Seguranca-do-Trabalho/snes-smart-home/hardware/01_SNES_BUS_AND_CIC.kicad_sch

## KiCad design hardware/01_SNES_BUS_AND_CIC.kicad_sch (2026-09-11)

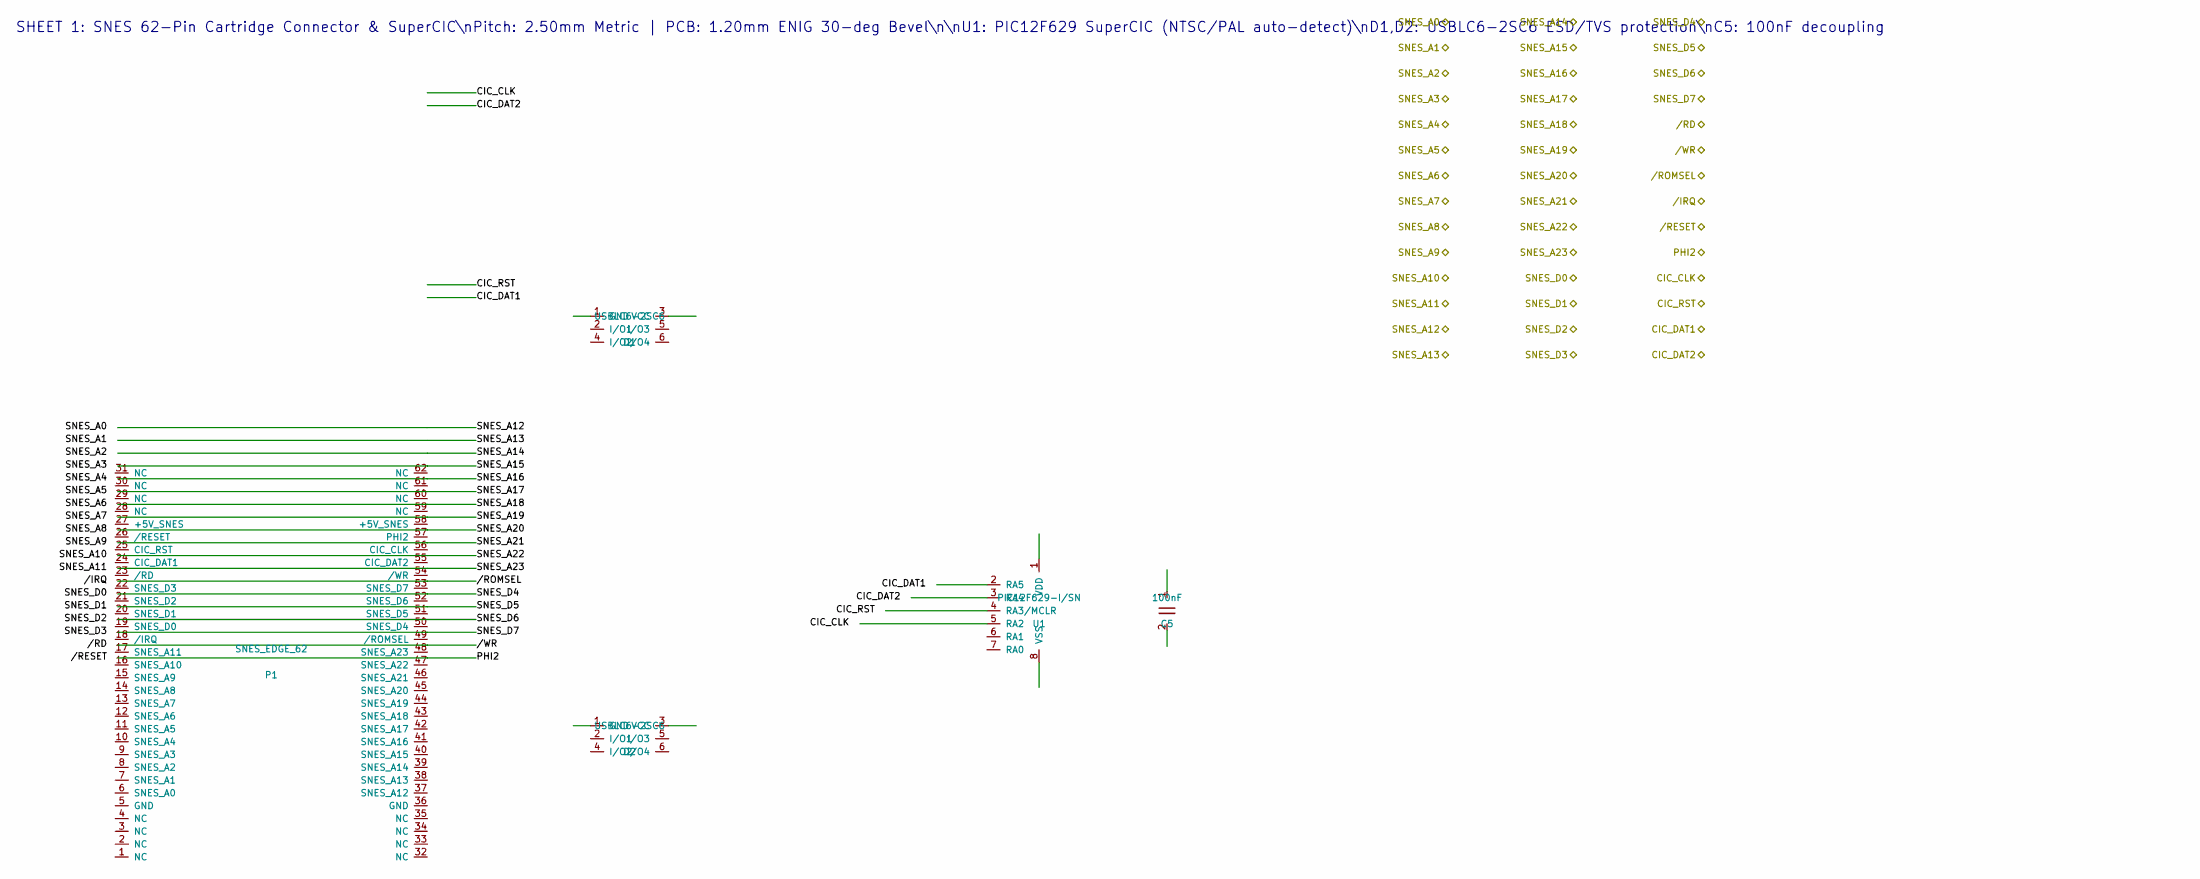
[picture p6: schematic 01_SNES_BUS_AND_CIC.kicad_sch]

Parts:
C5: 100nF; C_0402_1005Metric; LCSC C14663
D1, D2: USBLC6-2SC6; SOT-23-6_Handsoldering; LCSC C7519
P1: SNES_EDGE_62; SNES_CartridgeEdge_62Pin_2.50mm; LCSC Custom
U1: PIC12F629-I/SN; SOIC-8_3.9x4.9mm_P1.27mm; LCSC C20967

Notes on the sheet:
SHEET 1: SNES 62-Pin Cartridge Connector & SuperCIC\nPitch: 2.50mm Metric | PCB: 1.20mm ENIG 30-deg Bevel\n\nU1: PIC12F629 SuperCIC (NTSC/PAL auto-detect)\nD1,D2: USBLC6-2SC6 ESD/TVS protection\nC5: 100nF decoupling
