Seguranca-do-Trabalho/snes-smart-home/hardware/02_LEVEL_SHIFTERS_AND_FLASH.kicad_sch

## KiCad design hardware/02_LEVEL_SHIFTERS_AND_FLASH.kicad_sch (2026-09-11)

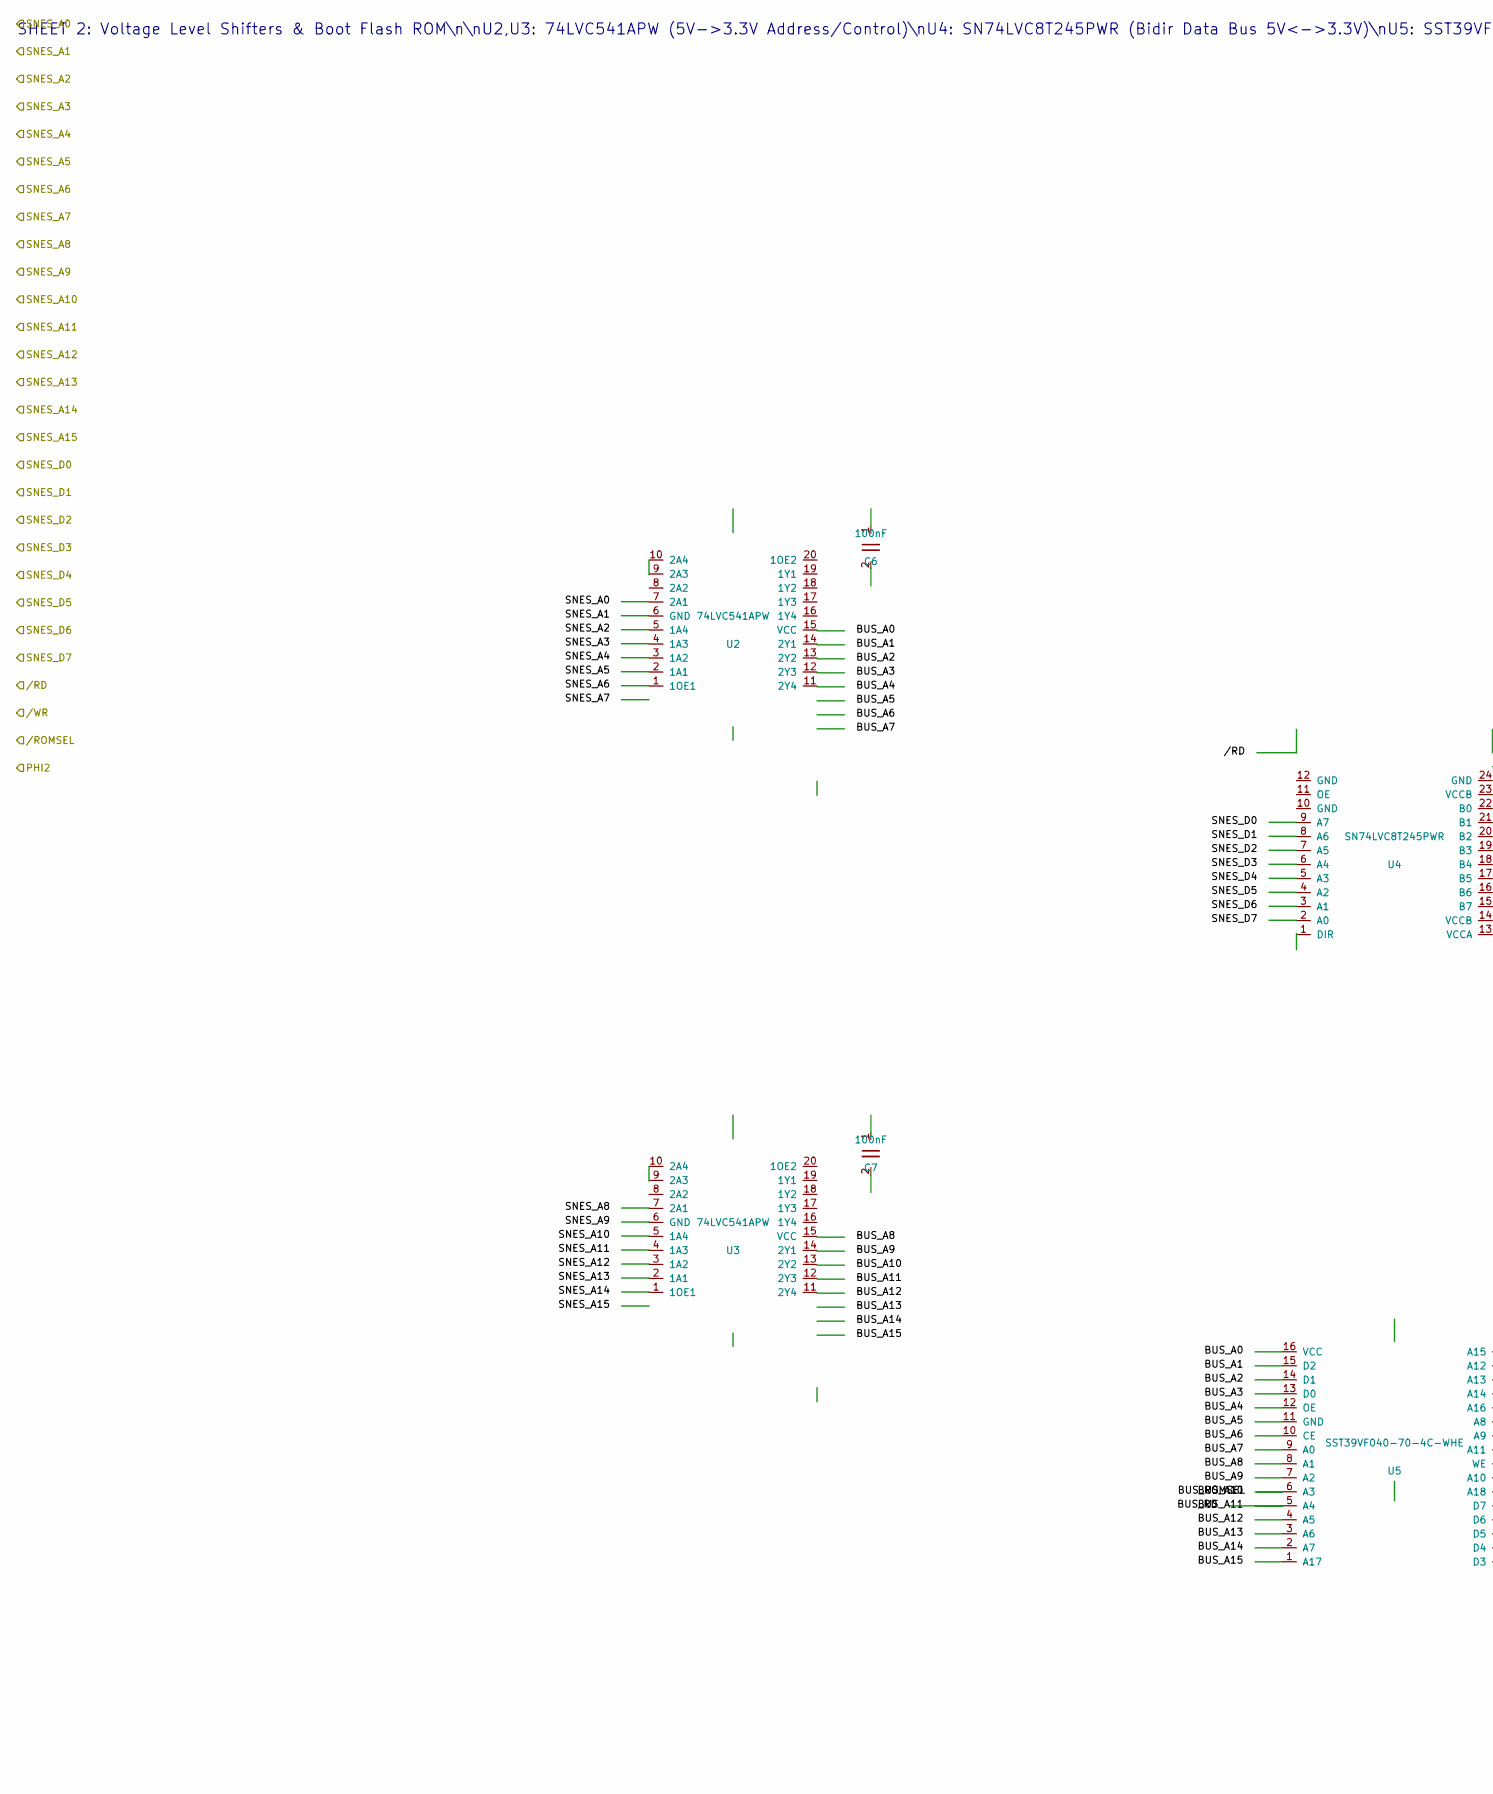
[picture p7: schematic 02_LEVEL_SHIFTERS_AND_FLASH.kicad_sch, part in row 1, column 1]

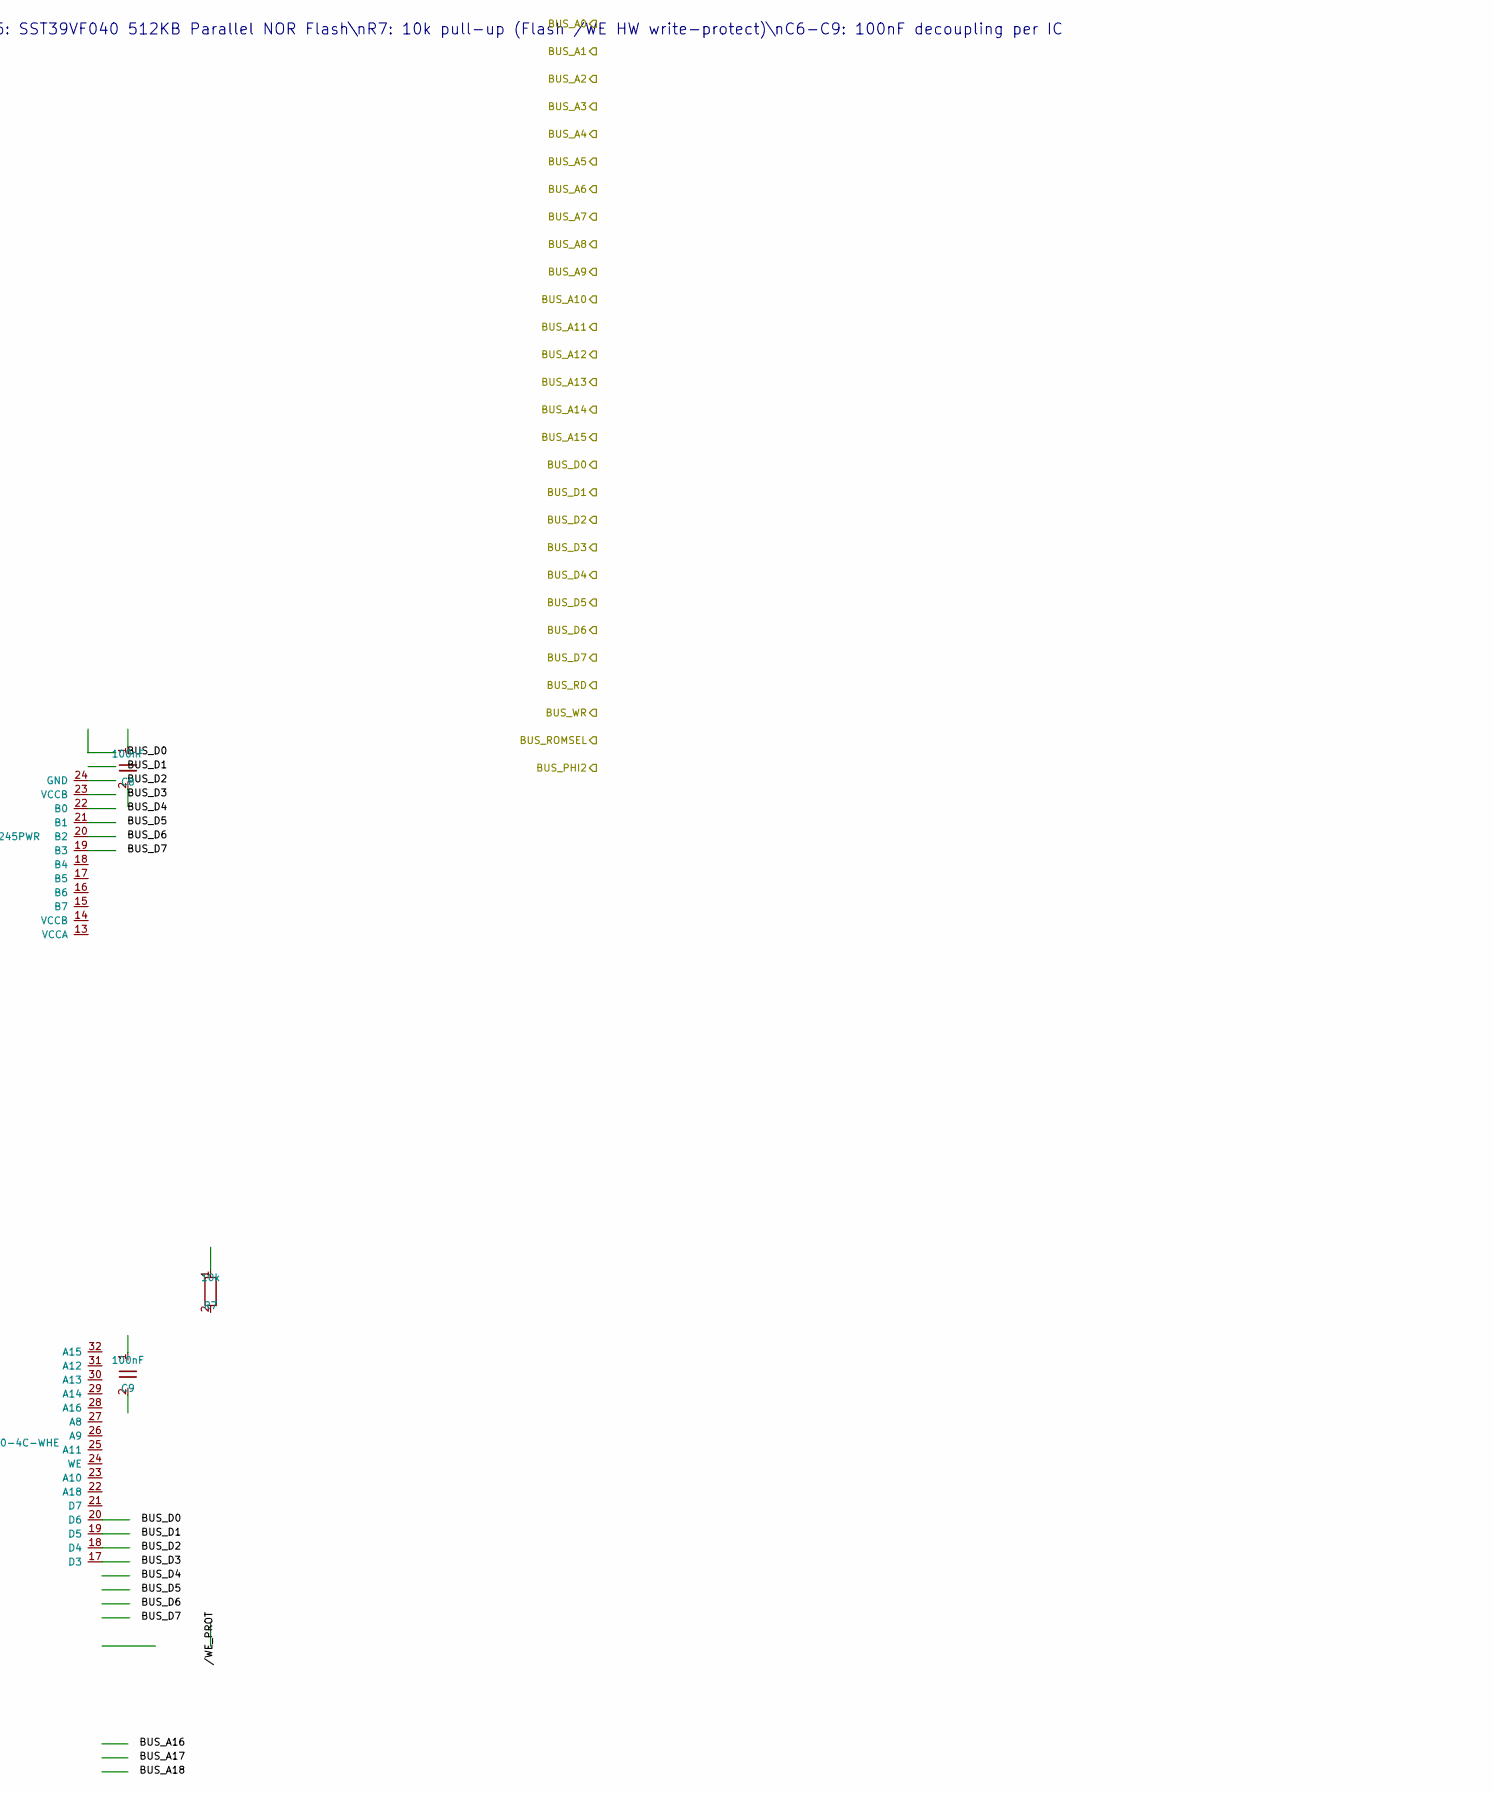
[picture p8: schematic 02_LEVEL_SHIFTERS_AND_FLASH.kicad_sch, part in row 1, column 2]

Parts:
C6, C7, C8, C9: 100nF; C_0402_1005Metric; LCSC C14663
R7: 10k; R_0402_1005Metric; LCSC C25804
U2, U3: 74LVC541APW; TSSOP-20_4.4x6.5mm_P0.65mm; LCSC C5975
U4: SN74LVC8T245PWR; TSSOP-24_4.4x7.8mm_P0.65mm; LCSC C6207
U5: SST39VF040-70-4C-WHE; TSOP-32_8x14mm_P0.5mm; LCSC C129525

Connections:
BUS_A11: U5.5 (A4)

Notes on the sheet:
SHEET 2: Voltage Level Shifters & Boot Flash ROM\n\nU2,U3: 74LVC541APW (5V->3.3V Address/Control)\nU4: SN74LVC8T245PWR (Bidir Data Bus 5V<->3.3V)\nU5: SST39VF040 512KB Parallel NOR Flash\nR7: 10k pull-up (Flash /WE HW write-protect)\nC6-C9: 100nF decoupling per IC
