Seguranca-do-Trabalho/snes-smart-home/hardware/03_RP2350_SUBSYSTEM.kicad_sch

## KiCad design hardware/03_RP2350_SUBSYSTEM.kicad_sch (2026-09-11)

Schematic: 03_RP2350_SUBSYSTEM.kicad_sch

Parts:
C10, C11: 15pF; C_0402_1005Metric; LCSC C1554
C12, C13, C18: 100nF; C_0402_1005Metric; LCSC C14663
C17: 10uF; C_0805_2012Metric; LCSC C15849
J1: TYPE-C-31-M-12; USB_C_Receptacle_HRO_TYPE-C-31-M-12; LCSC C165948
R3, R4: 5.1k; R_0402_1005Metric; LCSC C25905
R5, R6: 27R; R_0402_1005Metric; LCSC C25114
R8: 10k; R_0402_1005Metric; LCSC C25804
SW1: BOOTSEL; SW_SPST_TL3342; LCSC C318884
SW2: RESET; SW_SPST_TL3342; LCSC C318884
U6: RP2350B; QFN-80-1EP_10x10mm_P0.5mm_EP6.1x6.1mm; LCSC SC1409
U7: W25Q128JVSIQ; SOIC-8_3.9x4.9mm_P1.27mm; LCSC C97521
Y1: 12.000MHz; Crystal_SMD_3215-2Pin_3.2x1.5mm; LCSC C16280

Notes on the sheet:
SHEET 3: RP2350B Dual-Core MCU Subsystem\n\nU6: RP2350B (Cortex-M33 x2, 520KB SRAM)\nU7: W25Q128JVSIQ 16MB QSPI Flash\nY1: 12MHz crystal + 15pF load caps\nJ1: USB-C (UF2 drag-and-drop)\nSW1: BOOTSEL, SW2: RESET\nR3-R4: 5.1k USB-C CC pulldowns\nR5-R6: 27R USB series resistors\nR8: 10k QSPI CS pull-up
