Seguranca-do-Trabalho/snes-smart-home/hardware/04_ESP32C6_WIFI_IOT.kicad_sch

## KiCad design hardware/04_ESP32C6_WIFI_IOT.kicad_sch (2026-09-11)

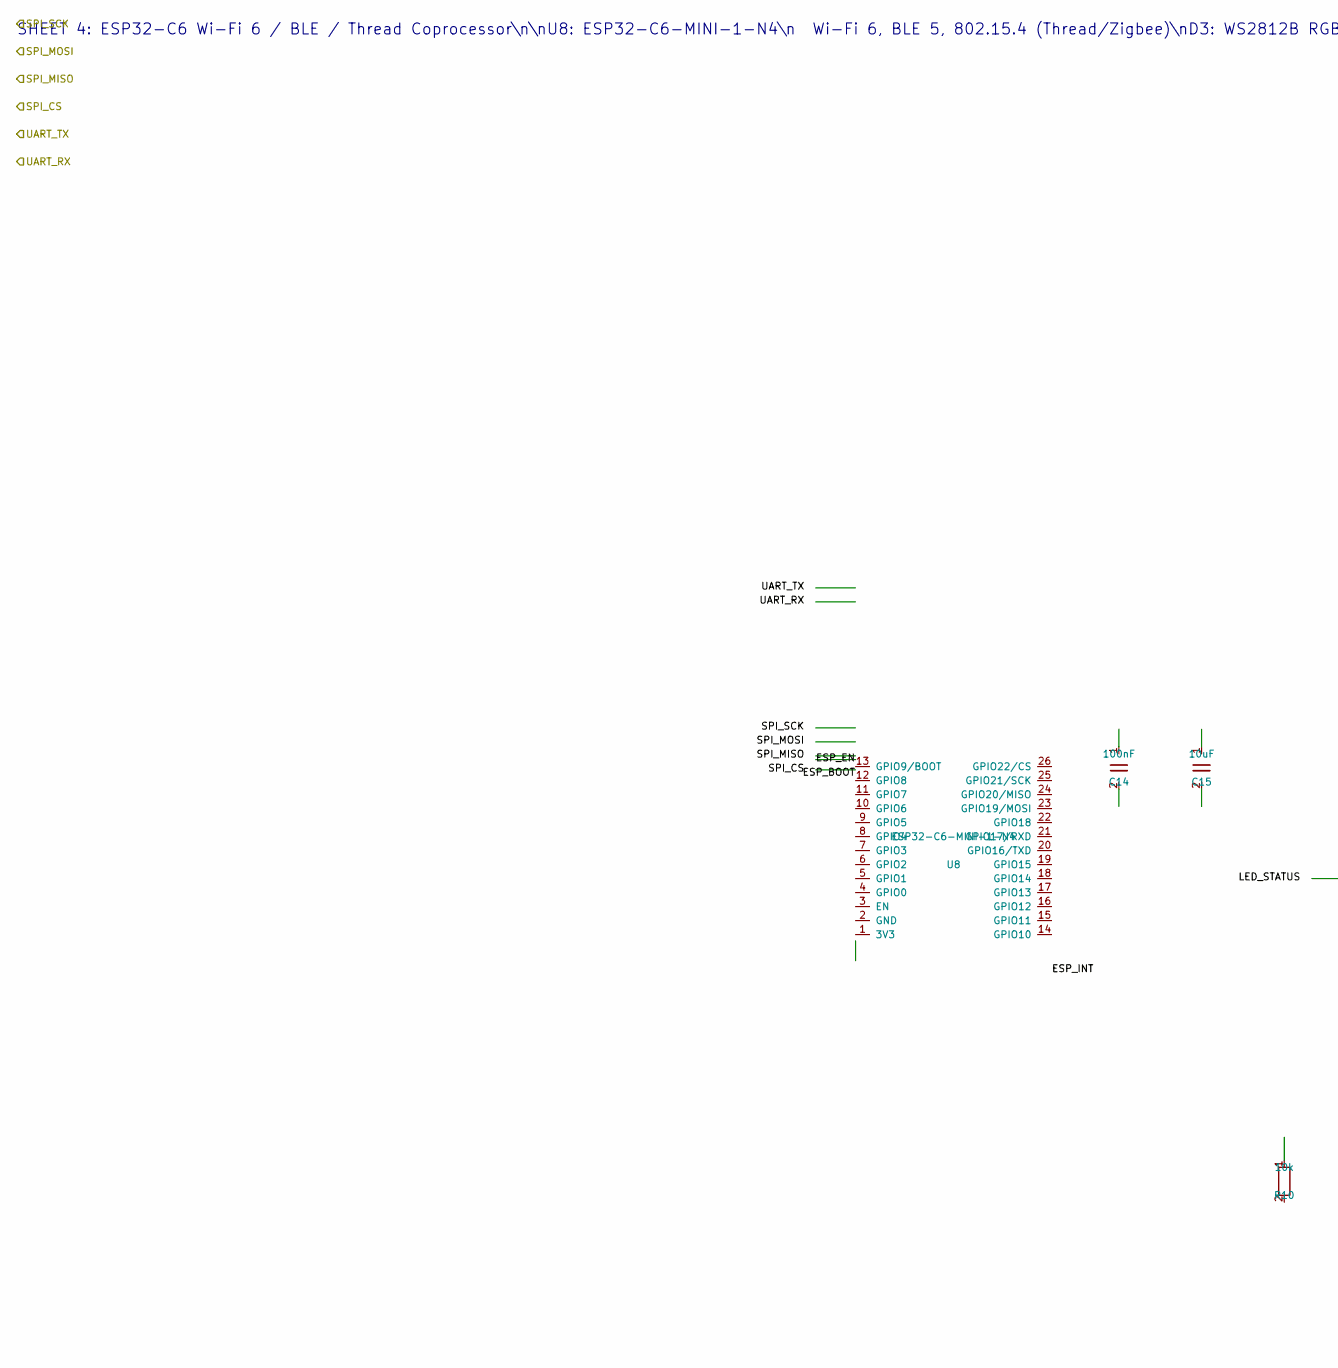
[picture p9: schematic 04_ESP32C6_WIFI_IOT.kicad_sch, part in row 1, column 1]

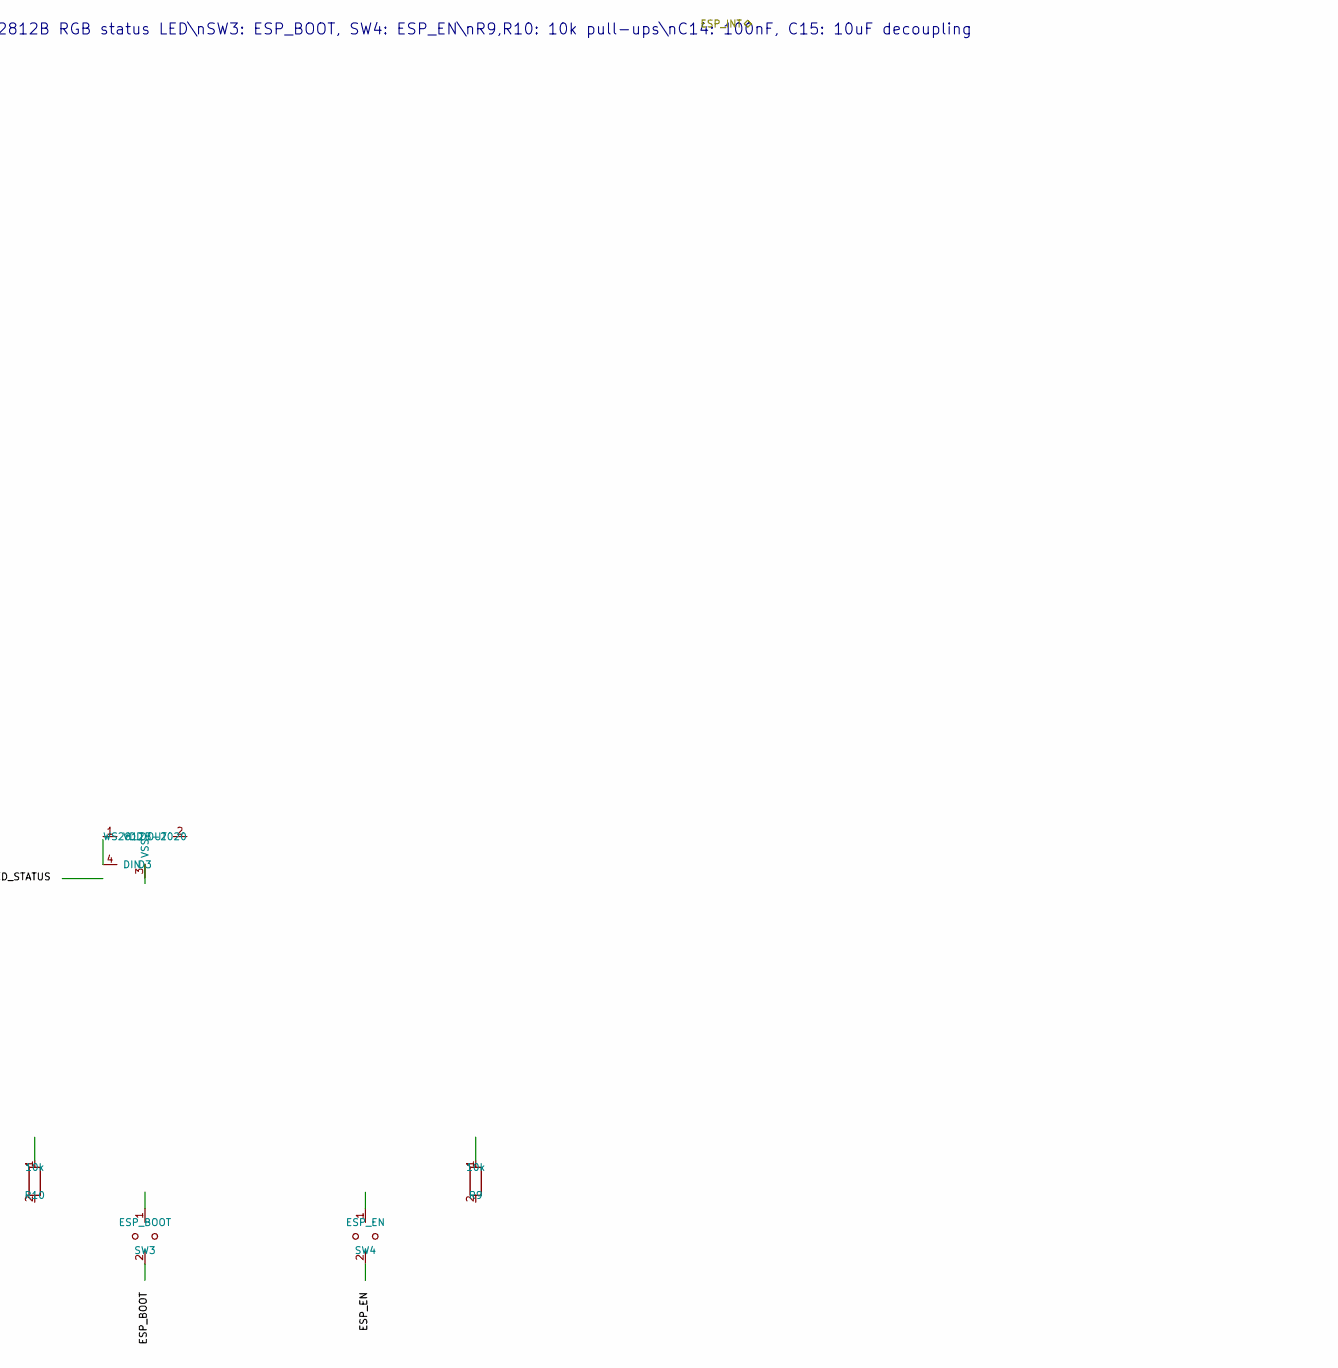
[picture p10: schematic 04_ESP32C6_WIFI_IOT.kicad_sch, part in row 1, column 2]

Parts:
C14: 100nF; C_0402_1005Metric; LCSC C14663
C15: 10uF; C_0805_2012Metric; LCSC C15849
D3: WS2812B-2020; LED_WS2812B_PLCC4_3.2x3.2mm_P1.75mm; LCSC C2890040
R9, R10: 10k; R_0402_1005Metric; LCSC C25804
SW3: ESP_BOOT; SW_SPST_TL3342; LCSC C318884
SW4: ESP_EN; SW_SPST_TL3342; LCSC C318884
U8: ESP32-C6-MINI-1-N4; ESP32-C6-MINI-1; LCSC C5248554

Notes on the sheet:
SHEET 4: ESP32-C6 Wi-Fi 6 / BLE / Thread Coprocessor\n\nU8: ESP32-C6-MINI-1-N4\n Wi-Fi 6, BLE 5, 802.15.4 (Thread/Zigbee)\nD3: WS2812B RGB status LED\nSW3: ESP_BOOT, SW4: ESP_EN\nR9,R10: 10k pull-ups\nC14: 100nF, C15: 10uF decoupling
