Seguranca-do-Trabalho/snes-smart-home/hardware/05_PERIPHERALS_AND_POWER.kicad_sch

## KiCad design hardware/05_PERIPHERALS_AND_POWER.kicad_sch (2026-09-11)

Schematic: 05_PERIPHERALS_AND_POWER.kicad_sch

Parts:
BT1: CR1220; BatteryHolder_CR1220_Holder; LCSC C70377
C1, C4: 47uF; C_1206_3216Metric; LCSC C13063
C2, C3: 22uF; C_0805_2012Metric; LCSC C15849
D4: SS34; D_SMA; LCSC C46104
F1: 1206L150PR; Fuse_1206_3216Metric; LCSC C70267
J4: TF-01A; TF_TF-01A; LCSC C91145
J5: KF2EDG-3.5-3P; TerminalBlock_bornier-3_P5.08mm; LCSC C8389
J6: JST_SH_1.0mm_4P; JST_SH_SM04B-SRSS-TB_1.00mm; LCSC C145920
L1: 2.2uH; L_0805_2012Metric; LCSC C144887
R1: 100k; R_0402_1005Metric; LCSC C25744
R2: 22k; R_0402_1005Metric; LCSC C25765
R11, R12: 4.7k; R_0402_1005Metric; LCSC C25900
R13, R14, R16, R17: 10k; R_0402_1005Metric; LCSC C25804
R15: 120R; R_0603_1608Metric; LCSC C22787
U9: SY8089AAAC; SOT-23-5_Handsoldering; LCSC C28674
U10: DS3231MZ+; SOIC-8_3.9x4.9mm_P1.27mm; LCSC C16719
U11: MAX3485; SOIC-8_3.9x4.9mm_P1.27mm; LCSC C6960

Notes on the sheet:
SHEET 5: Peripherals & 5V->3.3V Power Supply\n\nU9: SY8089AAAC Buck 5V->3.3V 2.0A (>92% eff)\nU10: DS3231MZ+ RTC (+-5ppm, battery backup)\nU11: MAX3485 RS-485 Transceiver\nD4: SS34 Schottky (reverse polarity)\nF1: PTC 1.5A (overcurrent)\nL1: 2.2uH inductor\nBT1: CR1220 battery holder
